jarrodbell/Bathroom-LED/pcb/Bathroom LED Controller_etch_silk_bottom.pdf

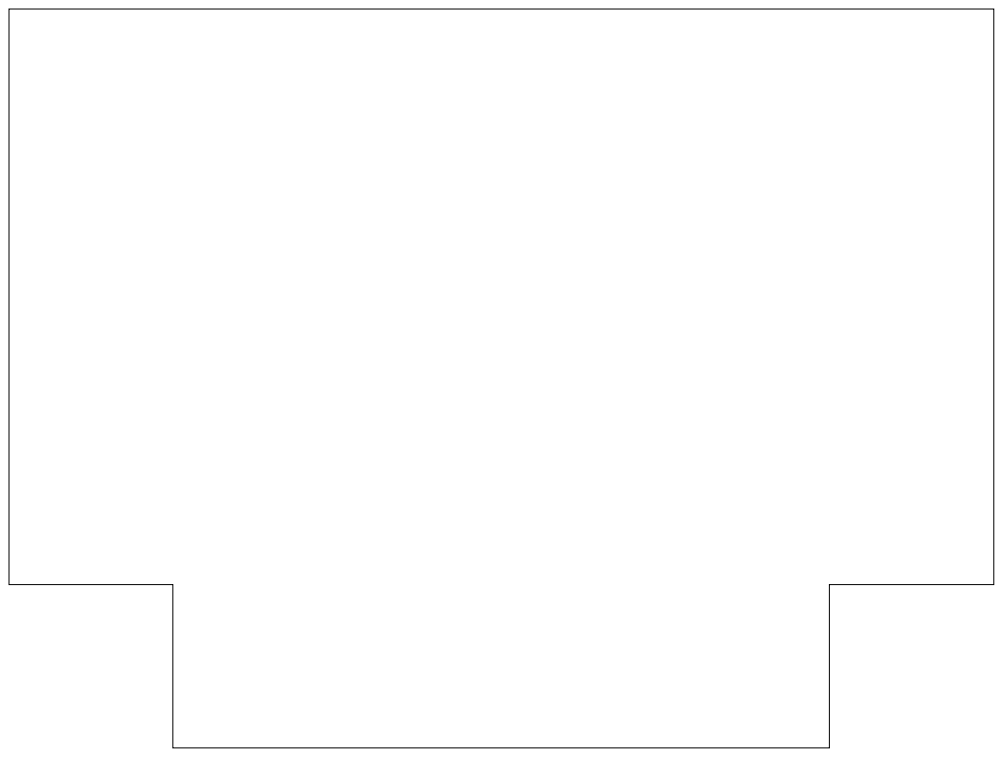
[picture p11: page 1]
