jarrodbell/Bathroom-LED/pcb/Bathroom LED Controller_etch_silk_bottom_mirror.pdf

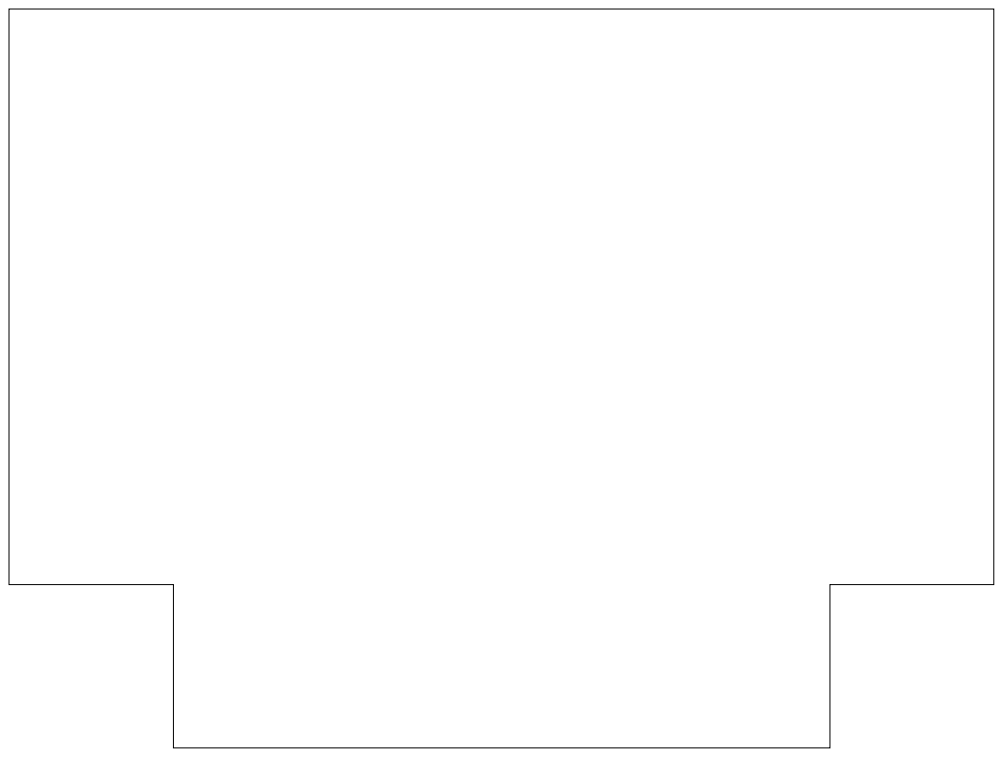
[picture p12: page 1]
