jarrodbell/Bathroom-LED/pcb/Bathroom LED Controller_etch_silk_top.pdf

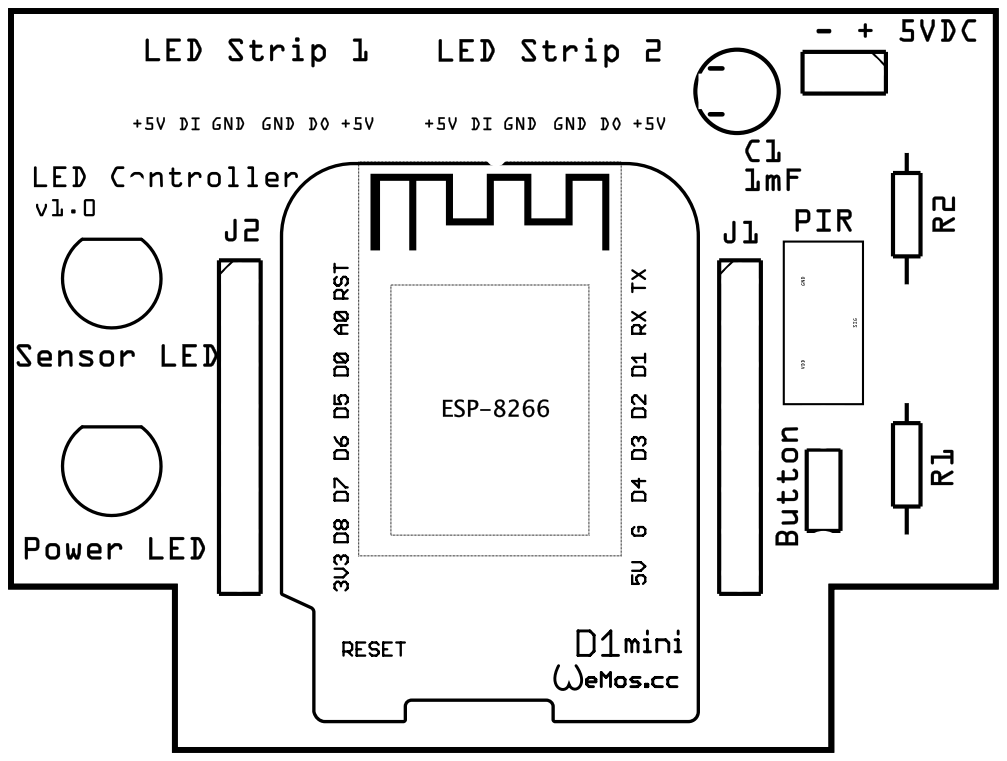
[picture p13: page 1]
