jarrodbell/Bathroom-LED/pcb/Bathroom LED Controller_etch_silk_top_mirror.pdf

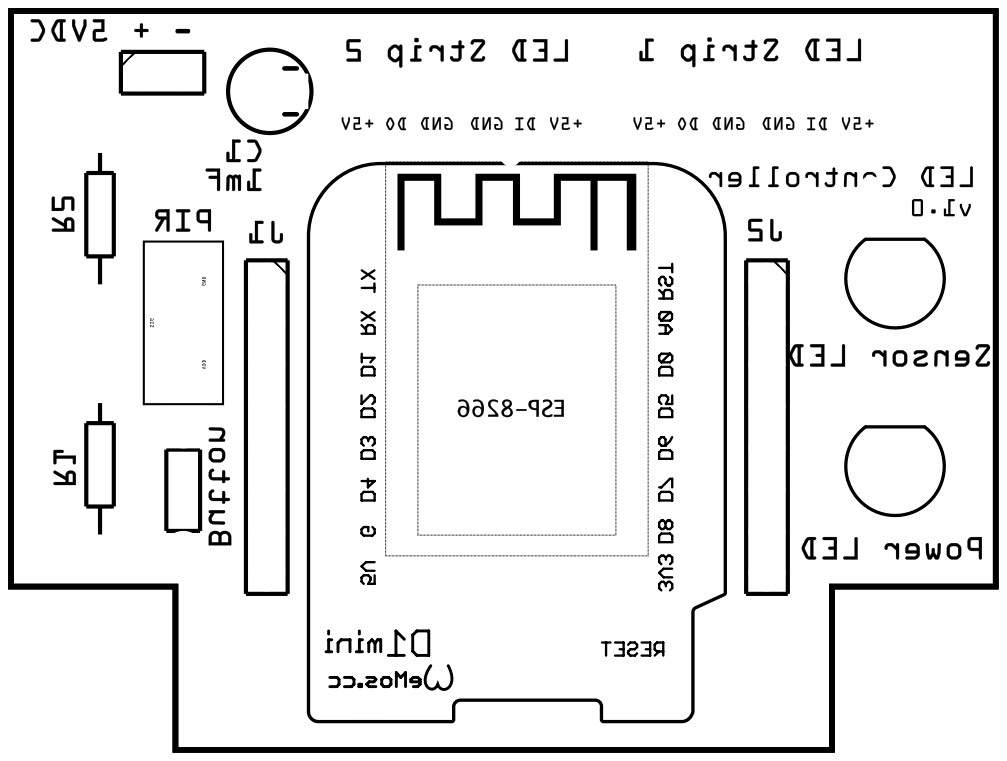
[picture p14: page 1]
