jarrodbell/Bathroom-LED/pcb/vertical-board/Bathroom LED Controller - vertical board_etch_copper_bottom.pdf

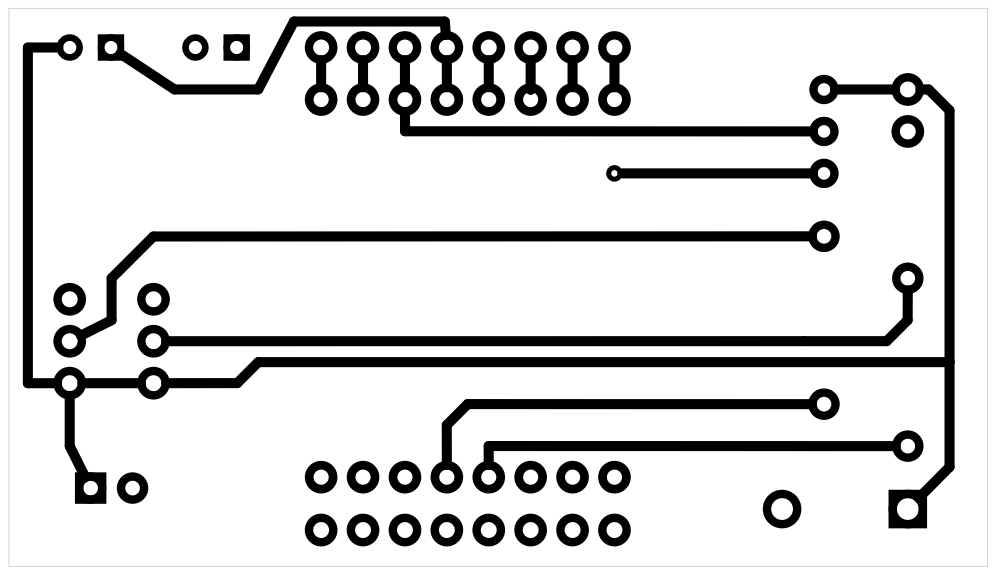
[picture p15: page 1]
