jarrodbell/Bathroom-LED/pcb/vertical-board/Bathroom LED Controller - vertical board_etch_copper_bottom_mirror.pdf

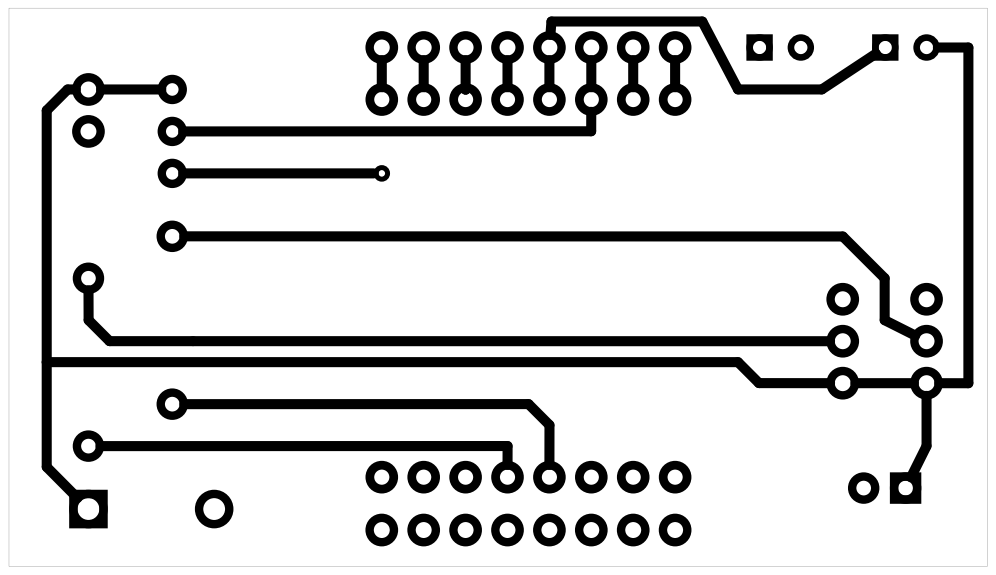
[picture p16: page 1]
