jarrodbell/Bathroom-LED/pcb/vertical-board/Bathroom LED Controller - vertical board_etch_copper_top.pdf

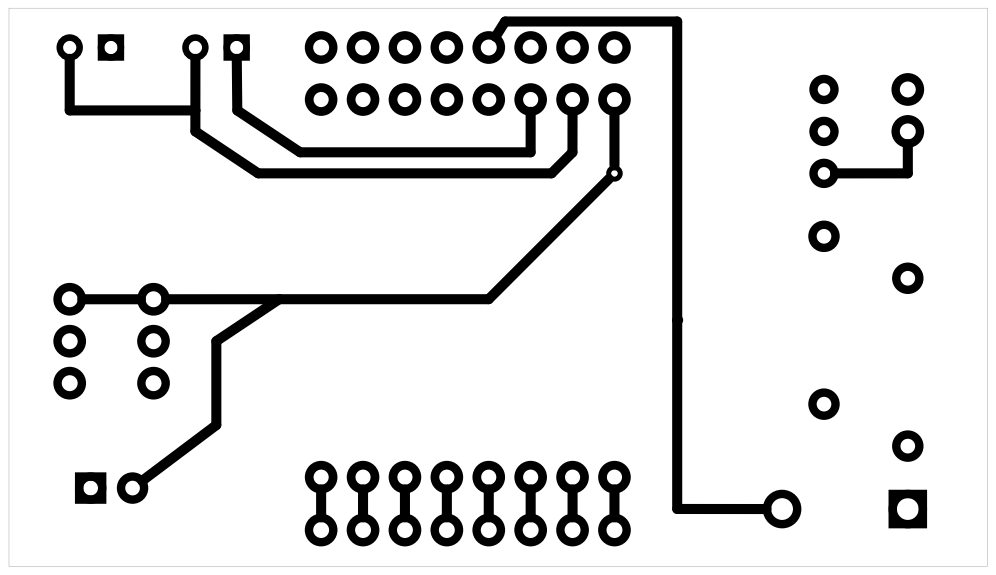
[picture p17: page 1]
