jarrodbell/Bathroom-LED/pcb/vertical-board/Bathroom LED Controller - vertical board_etch_copper_top_mirror.pdf

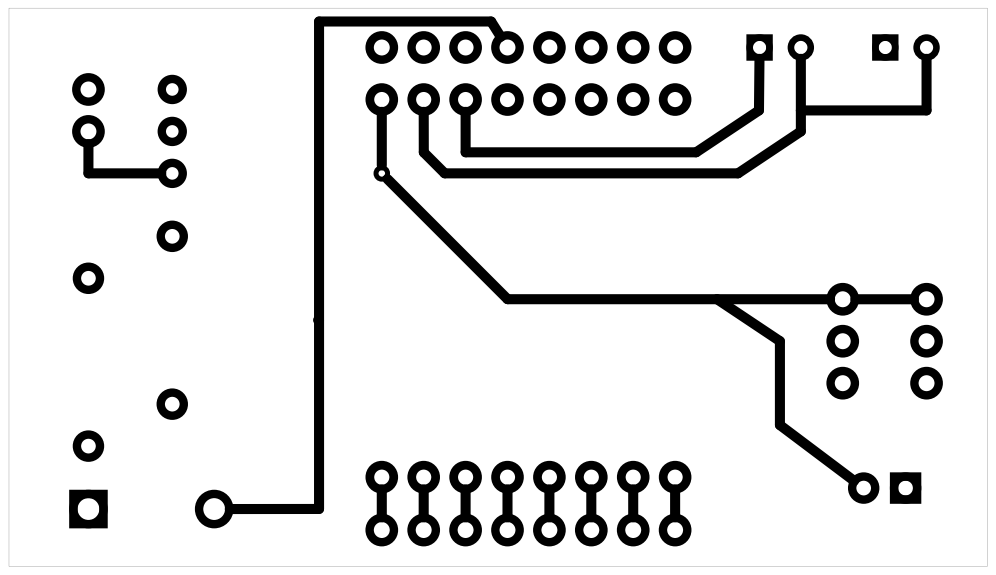
[picture p18: page 1]
