jarrodbell/Bathroom-LED/pcb/vertical-board/Bathroom LED Controller - vertical board_etch_mask_bottom.pdf

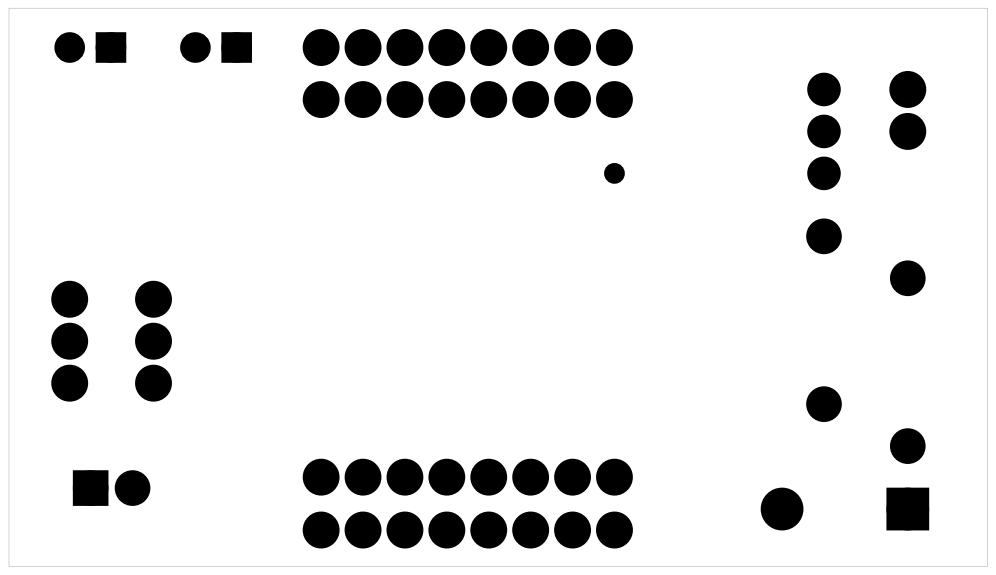
[picture p19: page 1]
