jarrodbell/Bathroom-LED/pcb/vertical-board/Bathroom LED Controller - vertical board_etch_mask_bottom_mirror.pdf

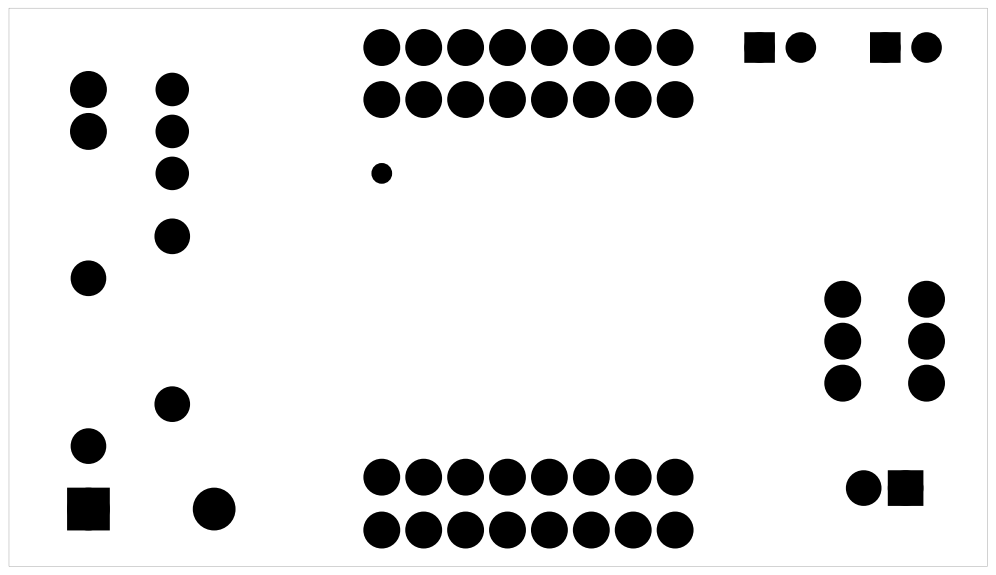
[picture p20: page 1]
