jarrodbell/Bathroom-LED/pcb/vertical-board/Bathroom LED Controller - vertical board_etch_silk_bottom.pdf

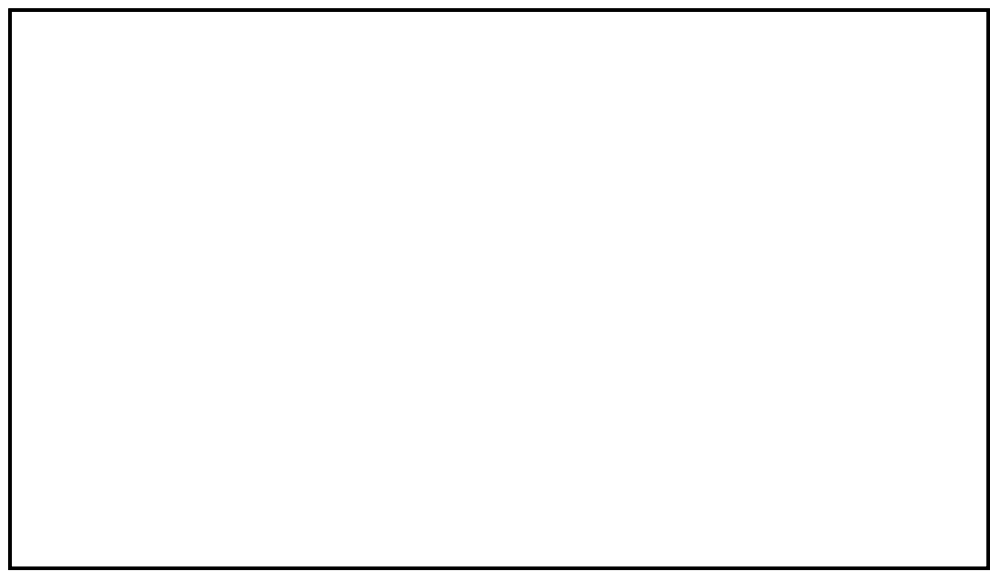
[picture p21: page 1]
