jarrodbell/Bathroom-LED/pcb/vertical-board/Bathroom LED Controller - vertical board_etch_silk_bottom_mirror.pdf

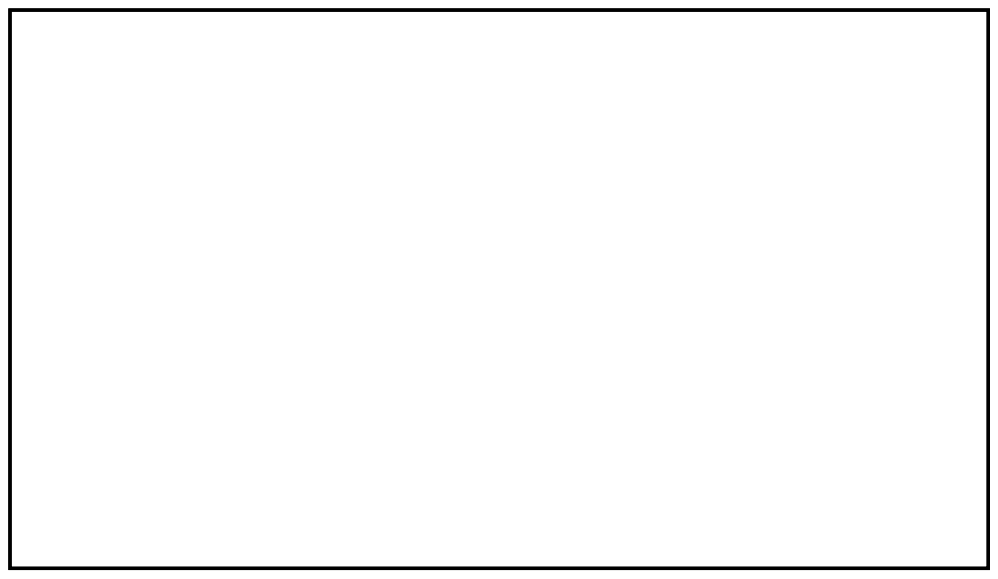
[picture p22: page 1]
