jarrodbell/Bathroom-LED/pcb/vertical-board/Bathroom LED Controller - vertical board_etch_silk_top.pdf

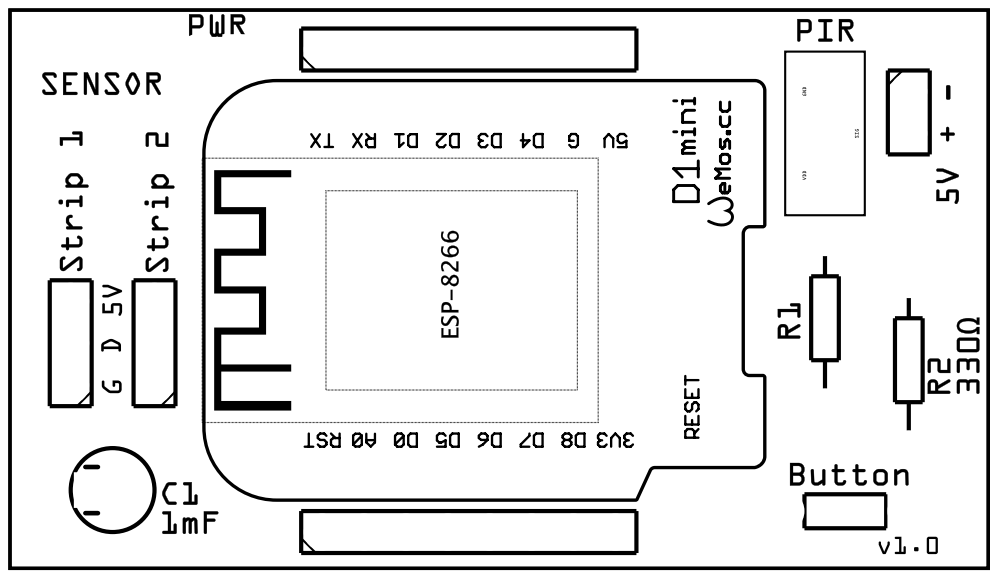
[picture p23: page 1]
