jarrodbell/Bathroom-LED/pcb/vertical-board/Bathroom LED Controller - vertical board_etch_silk_top_mirror.pdf

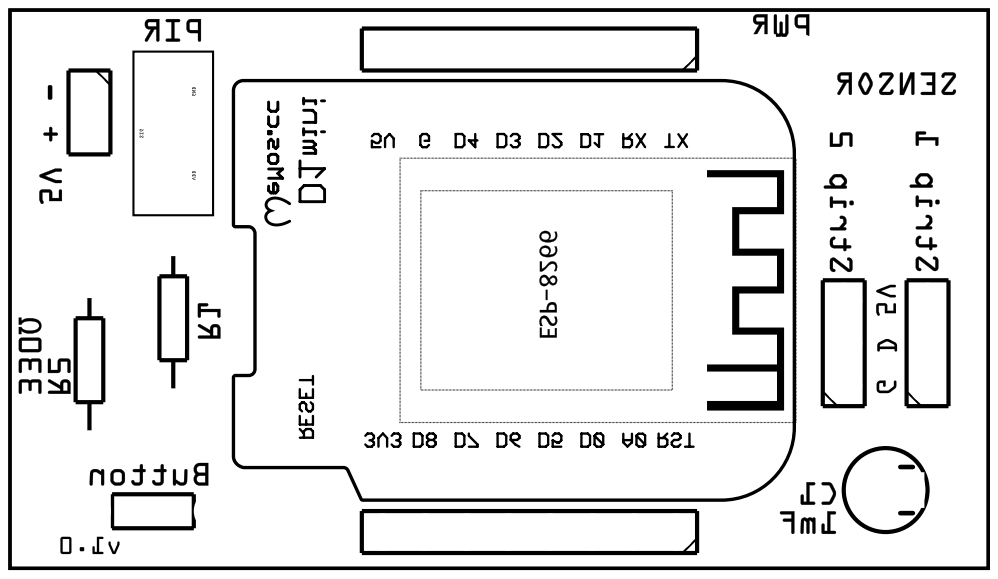
[picture p24: page 1]
